NEU-REAL/EverySync-Hardware-Suite/pic/Cover-OpenSource.png

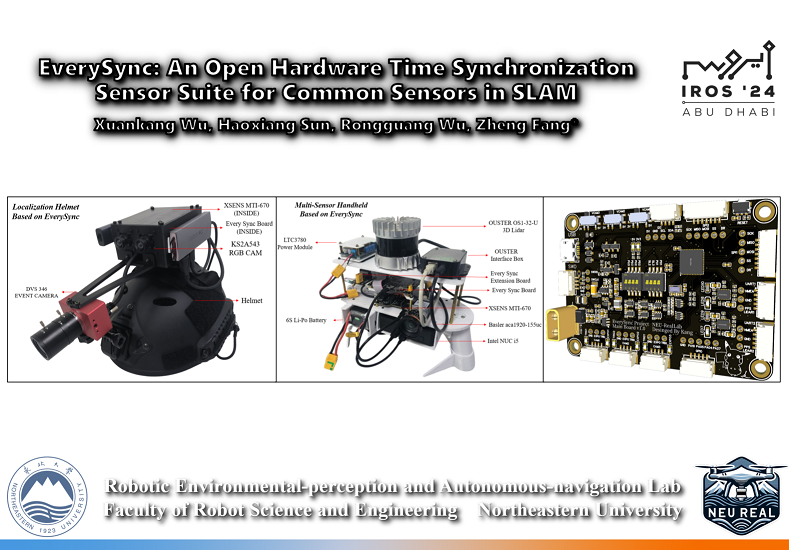
pic/Cover-OpenSource.png
