NEU-REAL/EverySync-Hardware-Suite/EverySync_PCB/Examples/0531_battery_cont.SLDPRT

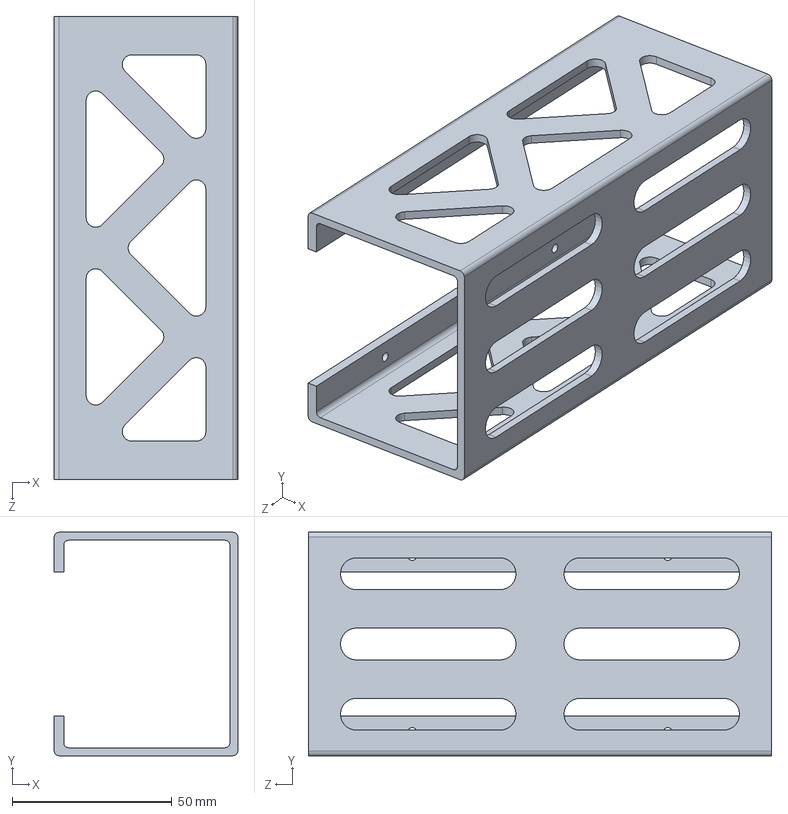
[picture p27: CAD file, 2025-01-12]
EverySync_PCB/Examples/0531_battery_cont.SLDPRT
57.5 x 70.0 x 145.0 mm
