NEU-REAL/EverySync-Hardware-Suite/EverySync_PCB/Examples/screenhold.SLDPRT

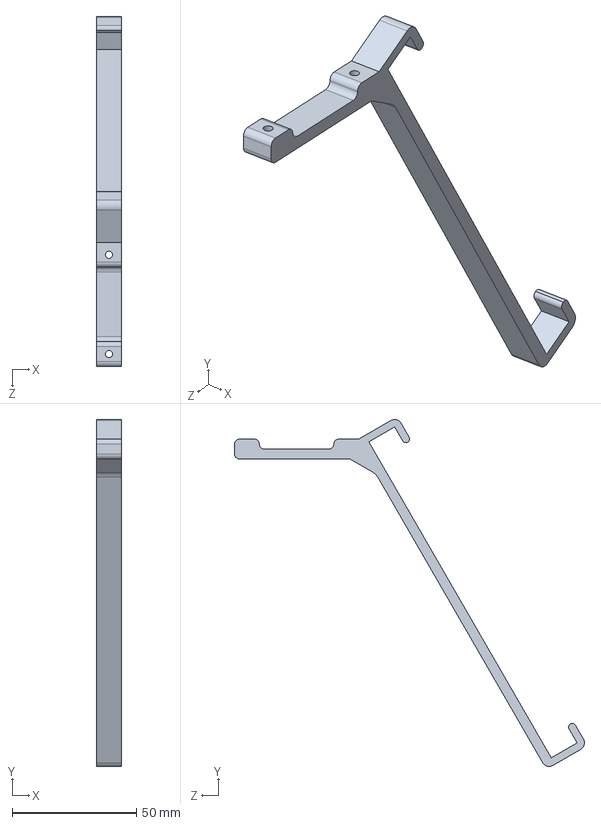
[picture p28: CAD file, 2025-01-12]
EverySync_PCB/Examples/screenhold.SLDPRT
10.0 x 139.7 x 140.9 mm
