NEU-REAL/EverySync-Hardware-Suite/EverySync_PCB/Examples/ouster.step.SLDPRT

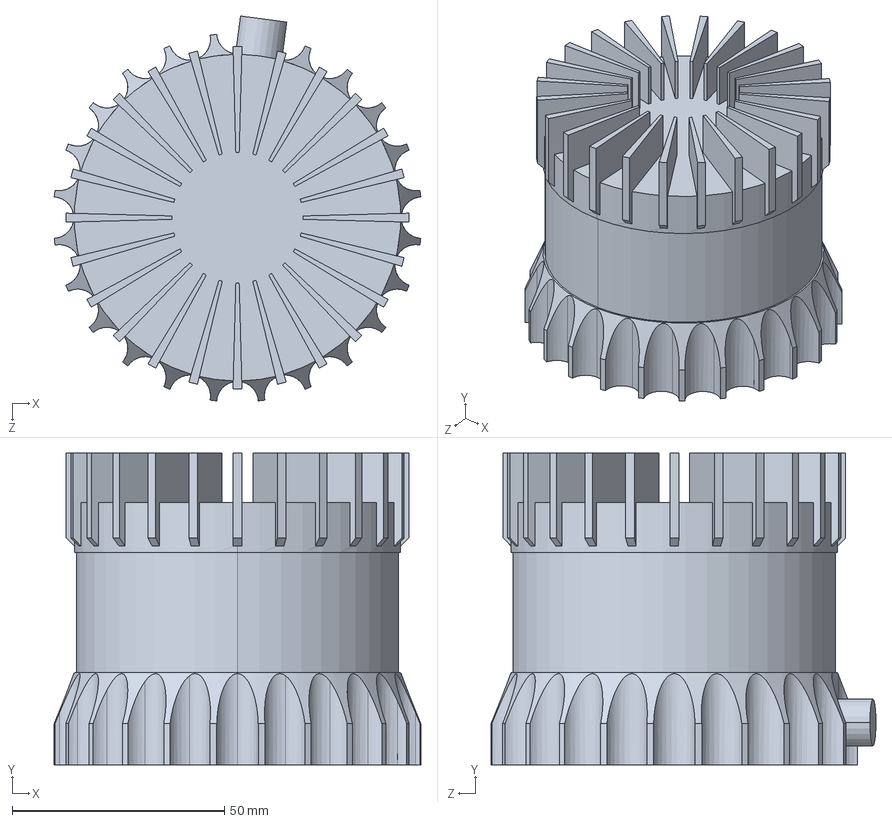
[picture p29: CAD file, 2025-01-12]
EverySync_PCB/Examples/ouster.step.SLDPRT
86.4 x 73.5 x 90.8 mm
