NEU-REAL/EverySync-Hardware-Suite/EverySync_PCB/Examples/battery_cont.SLDPRT

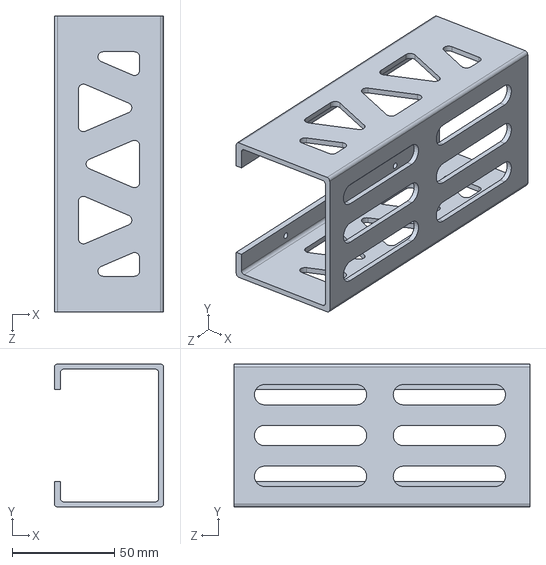
[picture p30: CAD file, 2025-01-12]
EverySync_PCB/Examples/battery_cont.SLDPRT
53.5 x 70.0 x 145.0 mm
