NEU-REAL/EverySync-Hardware-Suite/EverySync_PCB/Examples/support_v0731.SLDPRT

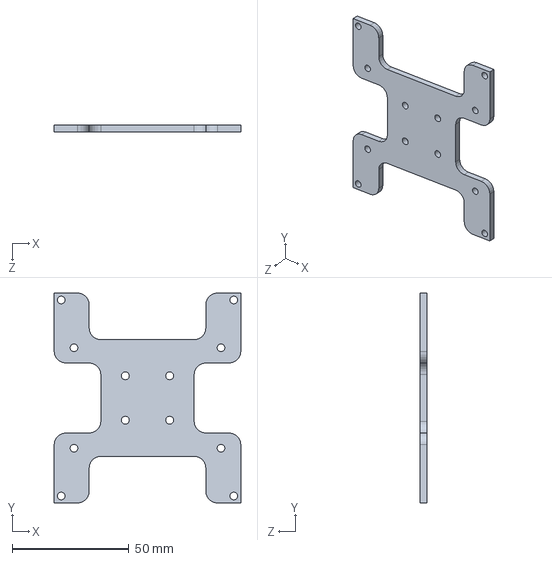
[picture p31: CAD file, 2025-01-12]
EverySync_PCB/Examples/support_v0731.SLDPRT
80.0 x 90.0 x 3.00 mm
