NEU-REAL/EverySync-Hardware-Suite/EverySync_PCB/Examples/handheld_base.SLDPRT

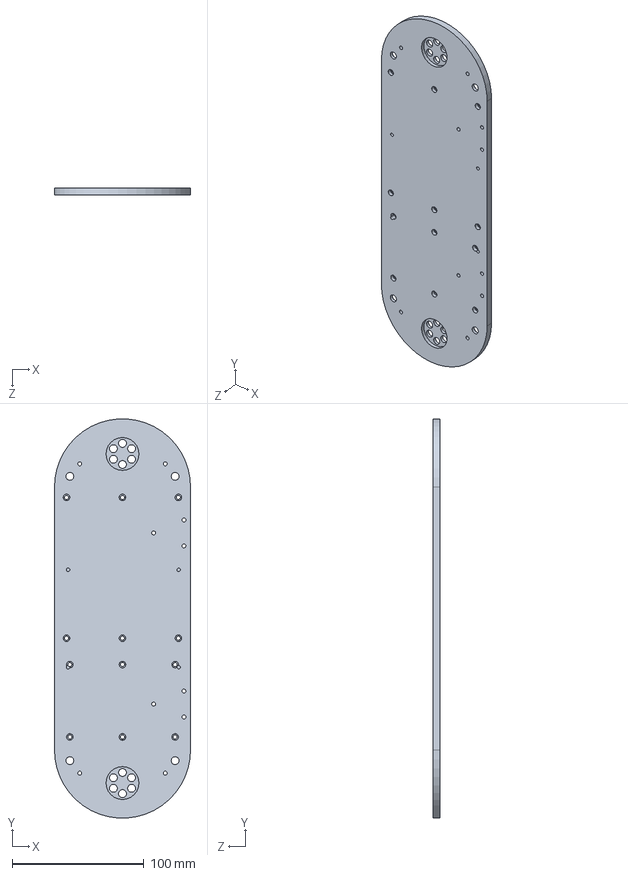
[picture p32: CAD file, 2025-01-12]
EverySync_PCB/Examples/handheld_base.SLDPRT
103.3 x 303.1 x 5.50 mm
