NEU-REAL/EverySync-Hardware-Suite/EverySync_PCB/Examples/3D_sync_ext_board.SLDPRT

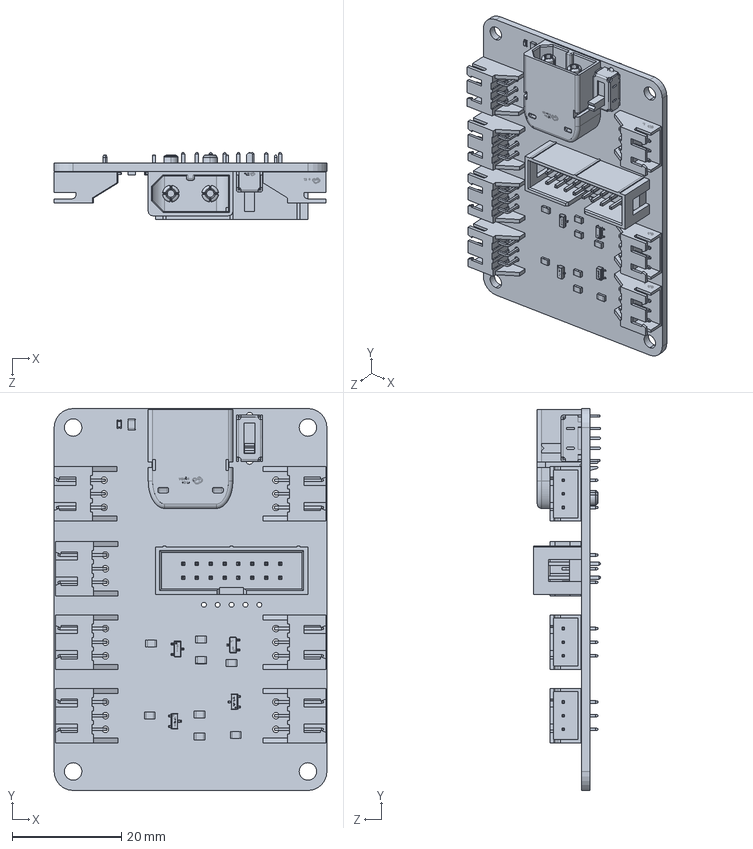
[picture p33: CAD file, 2025-01-12]
EverySync_PCB/Examples/3D_sync_ext_board.SLDPRT
50.0 x 70.0 x 12.3 mm
