NEU-REAL/EverySync-Hardware-Suite/EverySync_PCB/Examples/柱3×70.SLDPRT

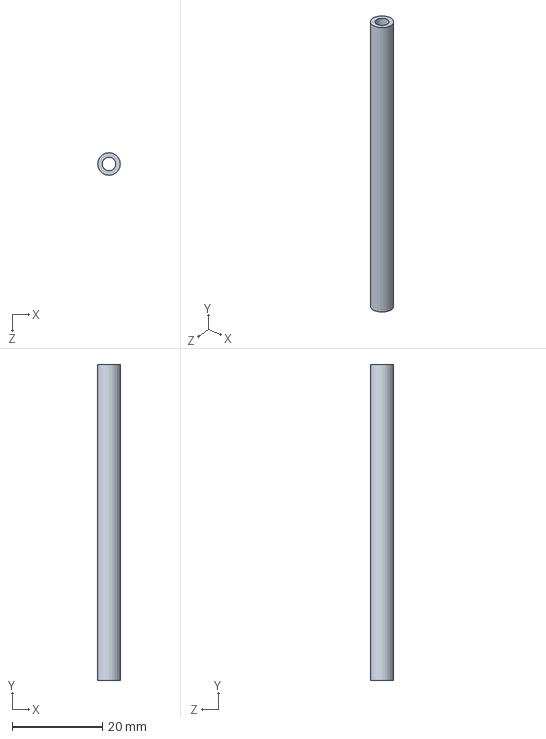
[picture p34: CAD file, 2025-01-12]
EverySync_PCB/Examples/柱3×70.SLDPRT
5.00 x 70.0 x 5.00 mm
