NEU-REAL/EverySync-Hardware-Suite/EverySync_PCB/Examples/battery6s.SLDPRT

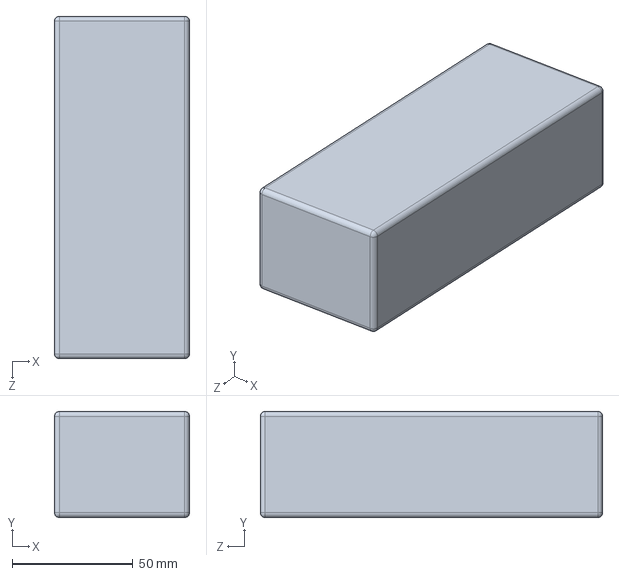
[picture p35: CAD file, 2025-01-12]
EverySync_PCB/Examples/battery6s.SLDPRT
56.0 x 44.0 x 142.0 mm
